NextBuilder/Atmosis/Images/23.png

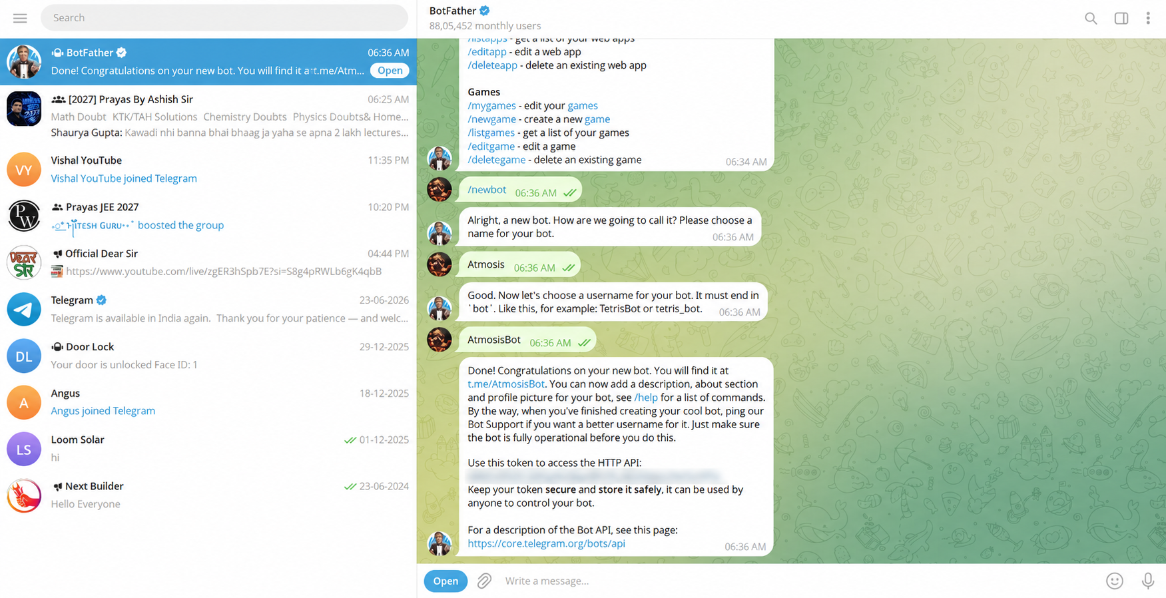
Images/23.png
